AdamLin0626/DrinksMachine/3D_OBJ/未來升級規劃/ProjectTest01_CanSilde.jpg

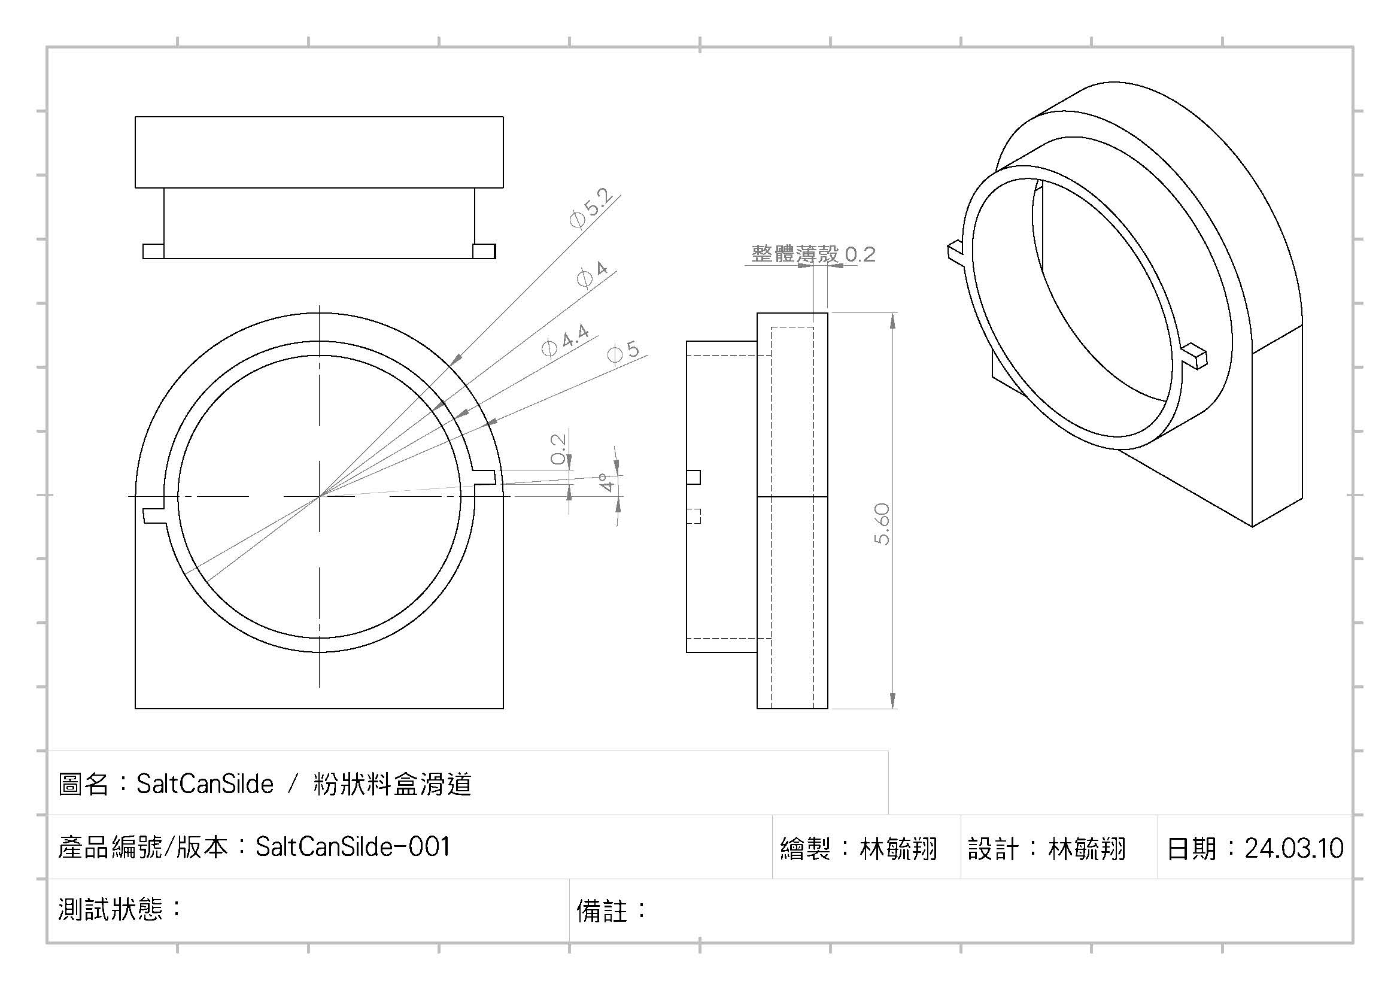
3D_OBJ/未來升級規劃/ProjectTest01_CanSilde.jpg
